jannin75/DesktopThing/ClockFace7.h

// 'ClockFace7', 240x240px - neon
// Created by LCD Image Converter using ColorR5G6B5 and Big_Endian
const uint16_t ClockFace7 [] PROGMEM = {
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
};
