jannin75/DesktopThing/minuteHandW.h

// Created by LCD Image Converter using ColorR5G6B5 and Little-Endian. Size is 7x100 with pivot at 8x79

const uint16_t minuteHandW [] PROGMEM = {
0x0000, 0x0000, 0x0000, 0x0000, 0x0000, 0x0000, 0x2000, 
0x2000, 0x0000, 0x0000, 0x0000, 0x0000, 0x0000, 0x0000, 
0x0000, 0x0000, 0xffff, 0xffff, 0xdfff, 0x0000, 0x2000, 
0x0000, 0x0000, 0xffff, 0xffff, 0xffff, 0x2000, 0x0000, 
0x0000, 0x0000, 0xffff, 0xdfff, 0xffff, 0x0000, 0x0000, 
0x0000, 0x0000, 0xffff, 0xffff, 0xdfff, 0x0000, 0x0000, 
0x0000, 0x2000, 0xffff, 0xdfff, 0xffff, 0x0000, 0x0000, 
0x0000, 0x0000, 0xffff, 0xffff, 0xffff, 0x0000, 0x2000, 
0x0000, 0x0000, 0xffff, 0xffff, 0xffff, 0x0000, 0x0000, 
0x0000, 0x0000, 0xffff, 0xffff, 0xffff, 0x0000, 0x0000, 
0x0000, 0x0000, 0xffff, 0xffff, 0xffff, 0x0000, 0x0000, 
0x0000, 0x0000, 0xffff, 0xffff, 0xffff, 0x0000, 0x0000, 
0x0000, 0x0000, 0xffff, 0xffff, 0xffff, 0x0000, 0x0000, 
0x0000, 0x0000, 0xffff, 0xffff, 0xffff, 0x0000, 0x0000, 
0x0000, 0x0000, 0xffff, 0xffff, 0xffff, 0x0000, 0x0000, 
0x0000, 0x0000, 0xffff, 0xffff, 0xffff, 0x0000, 0x0000, 
0x0000, 0x0000, 0xffff, 0xffff, 0xffff, 0x0000, 0x0000, 
0x0000, 0x0000, 0xffff, 0xffff, 0xffff, 0x0000, 0x0000, 
0x0000, 0x0000, 0xffff, 0xffff, 0xffff, 0x0000, 0x0000, 
0x0000, 0x0000, 0xffff, 0xffff, 0xffff, 0x0000, 0x0000, 
0x0000, 0x0000, 0xffff, 0xffff, 0xffff, 0x0000, 0x0000, 
0x0000, 0x0000, 0xffff, 0xffff, 0xffff, 0x0000, 0x0000, 
0x0000, 0x0000, 0xffff, 0xffff, 0xffff, 0x0000, 0x0000, 
0x0000, 0x0000, 0xffff, 0xffff, 0xffff, 0x0000, 0x0000, 
0x0000, 0x0000, 0xffff, 0xffff, 0xffff, 0x0000, 0x0000, 
0x0000, 0x0000, 0xffff, 0xffff, 0xffff, 0x0000, 0x0000, 
0x0000, 0x0000, 0xffff, 0xffff, 0xffff, 0x0000, 0x0000, 
0x0000, 0x0000, 0xffff, 0xffff, 0xffff, 0x0000, 0x0000, 
0x0000, 0x0000, 0xffff, 0xffff, 0xffff, 0x0000, 0x0000, 
0x0000, 0x0000, 0xffff, 0xffff, 0xffff, 0x0000, 0x0000, 
0x0000, 0x0000, 0xffff, 0xffff, 0xffff, 0x0000, 0x0000, 
0x0000, 0x0000, 0xffff, 0xffff, 0xffff, 0x0000, 0x0000, 
0x0000, 0x0000, 0xffff, 0xffff, 0xffff, 0x0000, 0x0000, 
0x0000, 0x0000, 0xffff, 0xffff, 0xffff, 0x0000, 0x0000, 
0x0000, 0x0000, 0xffff, 0xffff, 0xffff, 0x0000, 0x0000, 
0x0000, 0x0000, 0xffff, 0xffff, 0xffff, 0x0000, 0x0000, 
0x0000, 0x0000, 0xffff, 0xffff, 0xffff, 0x0000, 0x0000, 
0x0000, 0x0000, 0xffff, 0xffff, 0xffff, 0x0000, 0x0000, 
0x0000, 0x0000, 0xffff, 0xffff, 0xffff, 0x0000, 0x0000, 
0x0000, 0x0000, 0xffff, 0xffff, 0xffff, 0x0000, 0x0000, 
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
};
